johnnewman/watchtower/ancillary/case/v2/parts/v2_all_parts.stl

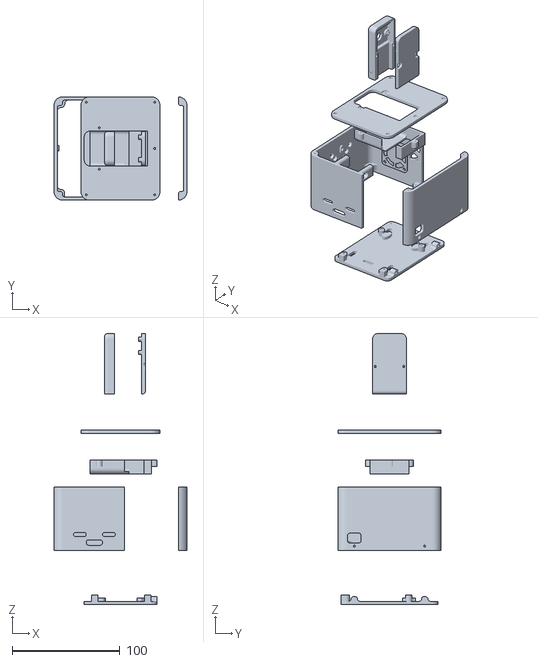
[picture p37: CAD file, 2020-08-12, an earlier design]
ancillary/case/v2/parts/v2_all_parts.stl
123.4 x 96.0 x 251.6
