johnnewman/watchtower/ancillary/case/v2/parts/v2_bottom.stl

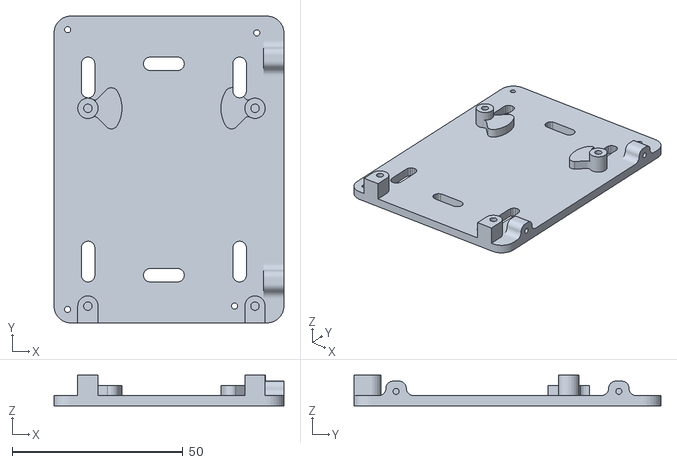
[picture p38: CAD file, 2020-08-12, an earlier design]
ancillary/case/v2/parts/v2_bottom.stl
67.4 x 90.0 x 9.00
